JasperCusiel/DIY-Split-Flap-Display/Enclosure 2.step

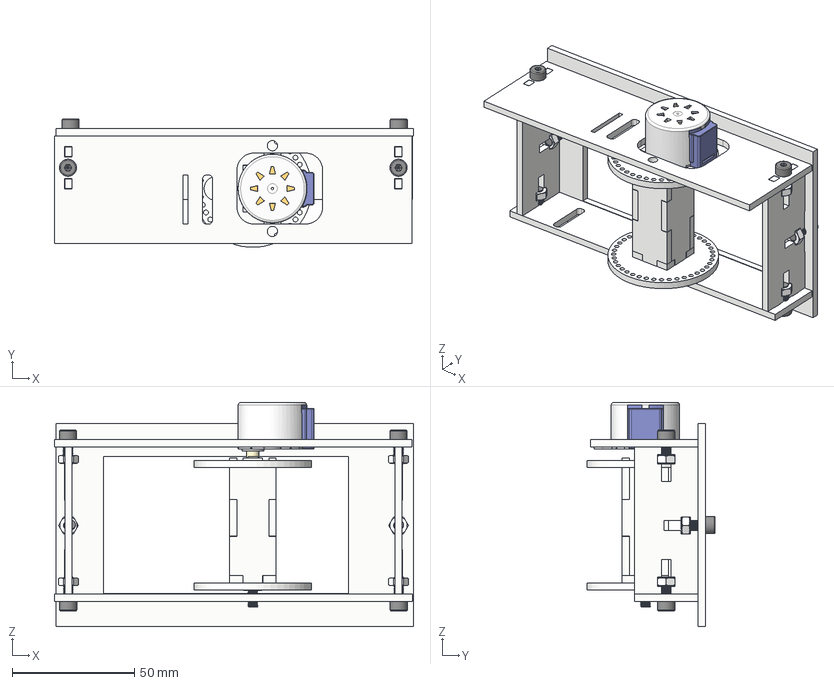
[picture p5: CAD file, 2021-09-17]
Enclosure 2.step
146.6 x 52.5 x 91.6 mm
28BYJ-48 v5
motor ring
screw ring
bolt holder
Center spacer 2
center spacer (1)
center spacer
Center spacer 2 (1)
Front plate
right plate
top
top (1)
motor plate
M4 bolt nut_7
M4 bolt nut_8
